doBeschte/py.console/py_console/Hardware/console/py_console.kicad_sch

## KiCad design py_console/Hardware/console/py_console.kicad_sch (2026-01-15)

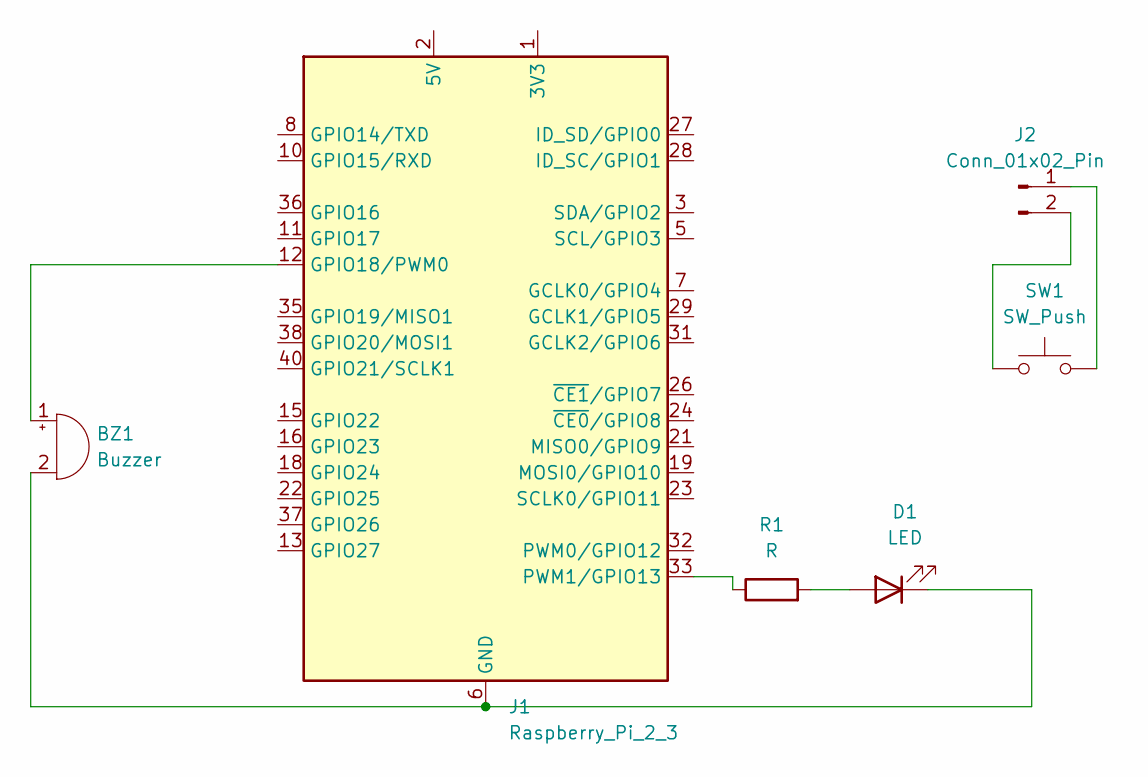
[picture p9: schematic py_console.kicad_sch]

Parts:
BZ1: Buzzer; PinHeader_1x02_P2.54mm_Horizontal
D1: LED; LED_D5.0mm
J1: Raspberry_Pi_2_3; PinHeader_2x20_P2.54mm_Vertical
J2: Conn_01x02_Pin; PinHeader_1x02_P2.54mm_Vertical
R1: R
SW1: SW_Push

Connections:
unnamed: BZ1.1 (+), J1.12 (GPIO18/PWM0)
unnamed: BZ1.2 (-), D1.1 (K), J1.6 (GND), J1.9 (GND), J1.14 (GND), J1.20 (GND), J1.25 (GND), J1.30 (GND), J1.34 (GND), J1.39 (GND)
unnamed: D1.2 (A), R1.2
unnamed: J1.1 (3V3), J1.17 (3V3)
unnamed: J1.2 (5V), J1.4 (5V)
unnamed: J1.33 (PWM1/GPIO13), R1.1
unnamed: J2.1, SW1.2
unnamed: J2.2, SW1.1
